X-ANONYMOUS-POWER-AMPLIFIER/X-B350W-4-LITE/3D-FOOTPRINTS/NTC.step

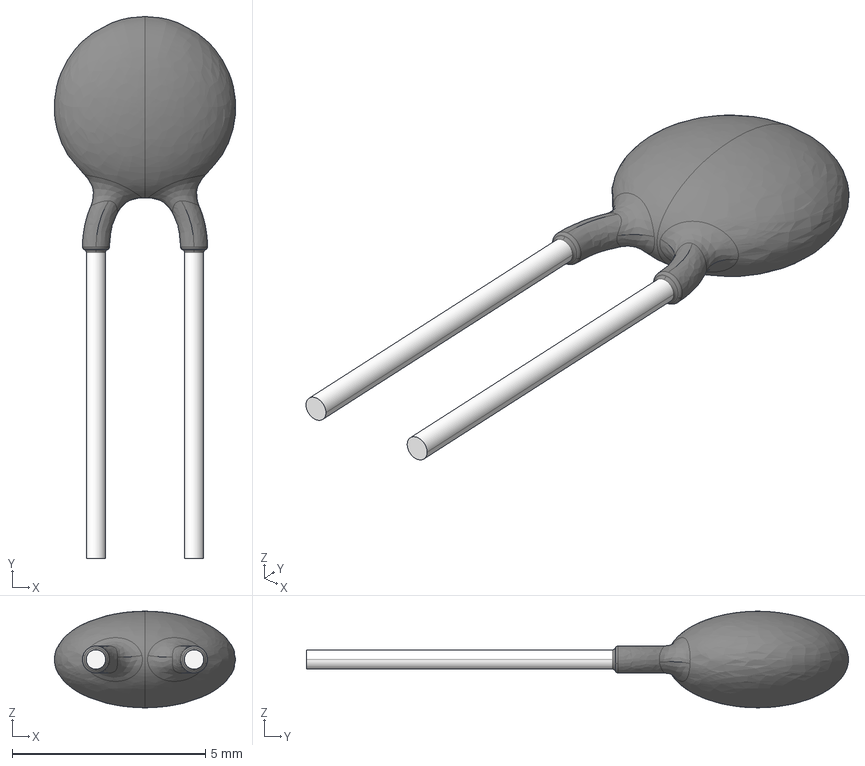
[picture p25: CAD file, 2026-05-19]
3D-FOOTPRINTS/NTC.step
4.70 x 14.0 x 2.50 mm
