X-ANONYMOUS-POWER-AMPLIFIER/X-B350W-4-LITE/3D-FOOTPRINTS/470uF 25V electr 8 x16mm -P.diameter 4mm-Black-White.stp

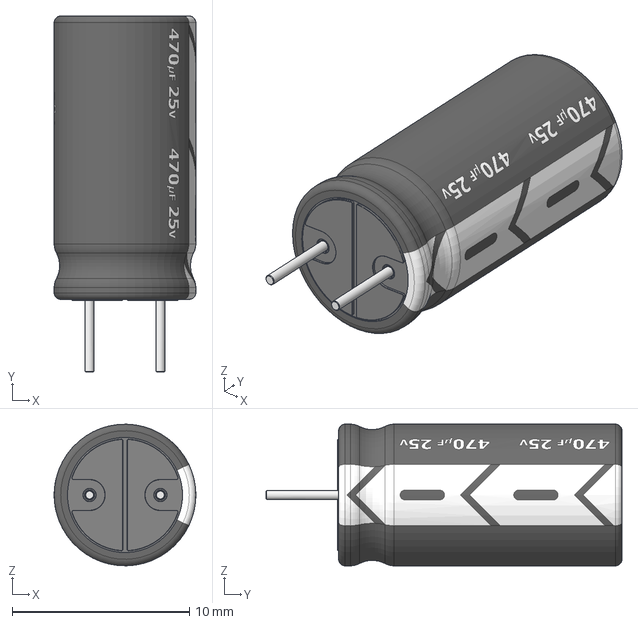
[picture p26: CAD file, 2026-05-19]
3D-FOOTPRINTS/470uF 25V electr 8 x16mm -P.diameter 4mm-Black-White.stp
8.00 x 20.1 x 8.00 mm
